jharris1993/PCIe_Floppy_Interface/Reference_Documentation/Research/README.md

# Research

This directory contains project-created research derived from external sources.

Research does not become a current project requirement or design merely because it is recorded here or discussed in `Project_Decisions/`. Current requirements and design are expressed in `Requirements.md` and `Design.md`, respectively.
