jharris1993/PCIe_Floppy_Interface/Reference_Implementations/Greaseweazle/Wiki_Snapshot/assets/f7_slim/F7_Slim_BoM.pdf

## Bill Of Materials for Greaseweazle F7 Basic

Design Title | Greaseweazle F7 Basic
Author | George Rudolf Mezzomo
Document Number | 01
Revision | 2.0
Design Created | segunda-feira, 10 de fevereiro de 2020
Design Last Modified sábado, 19 de dezembro de 2020

### Total Parts In Design 27

0 Modules
Quantity | References | Value
Sub-totals:
15 Capacitors
Quantity | References | Value
9 | C1-C2,C4,C6,C10-C14 | 100n
1 | C3 | 4.7u
3 | C5,C7-C8 | 1.0u
2 | C9,C15 | 10u
Sub-totals:
3 Resistors
Quantity | References | Value
2 | R1-R2 | CAY16
1 | R4 | 470
Sub-totals:
2 Integrated Circuits
Quantity | References | Value
1 | U1 | STM32F730R8T6
1 | U2 | AP2112K-3
Sub-totals:
0 Transistors
Quantity | References | Value
Sub-totals:
0 Diodes
Quantity | References | Value
Sub-totals:
7 Miscellaneous
Quantity | References | Value
1 | ACT | DIODE-LED
1 | DEBUG | CONN-SIL7
1 | J1 | 52271-2669
2 | RESET,WRITE INHIBIT | CONN-SIL2
1 | USB1 | 61729-0010BLF
1 | XO1 | ECS-3225MV-160-BN-TR
Sub-totals:

Totals:

| | sábado, 19 de dezembro de 2020 09:44:36
