jharris1993/PCIe_Floppy_Interface/Reference_Implementations/Greaseweazle/Wiki_Snapshot/assets/adapter_rev1/04_pill_headers.jpg

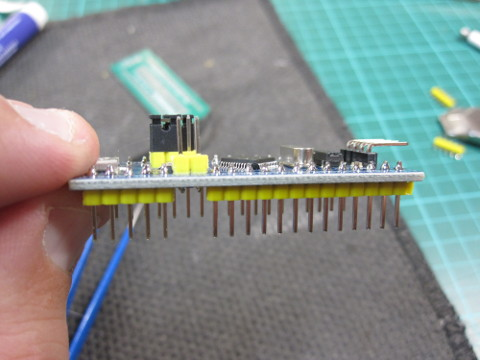
Reference_Implementations/Greaseweazle/Wiki_Snapshot/assets/adapter_rev1/04_pill_headers.jpg
