jharris1993/PCIe_Floppy_Interface/Reference_Implementations/Greaseweazle/Wiki_Snapshot/assets/f7_lightning/00_board.jpg

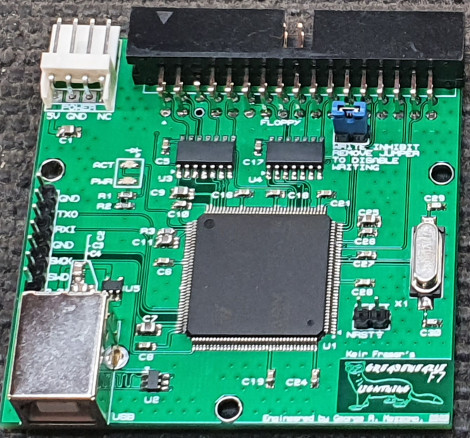
Reference_Implementations/Greaseweazle/Wiki_Snapshot/assets/f7_lightning/00_board.jpg
