jharris1993/PCIe_Floppy_Interface/Reference_Implementations/Greaseweazle/Wiki_Snapshot/assets/f7_lightning_plus/WIN_20200910_11_37_35_Pro.jpg

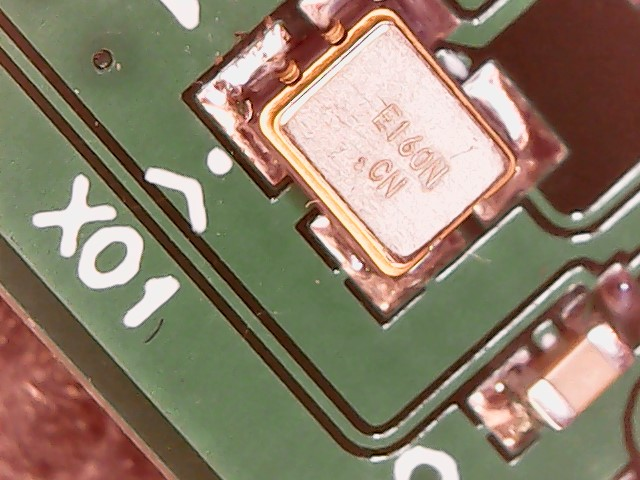
Reference_Implementations/Greaseweazle/Wiki_Snapshot/assets/f7_lightning_plus/WIN_20200910_11_37_35_Pro.jpg
