jharris1993/PCIe_Floppy_Interface/Reference_Implementations/Greaseweazle/Wiki_Snapshot/assets/ibmpc_ribbon.jpg

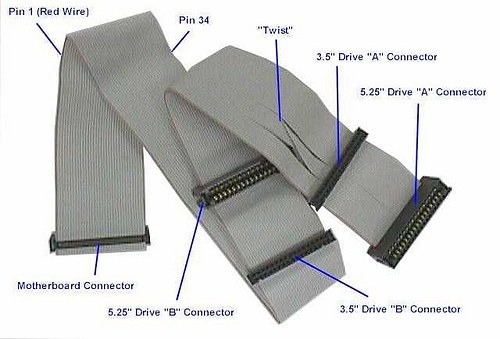
Reference_Implementations/Greaseweazle/Wiki_Snapshot/assets/ibmpc_ribbon.jpg
