jharris1993/PCIe_Floppy_Interface/Reference_Implementations/Greaseweazle/Wiki_Snapshot/assets/adapter_rev1/05_pill_soldered_inuse.jpg

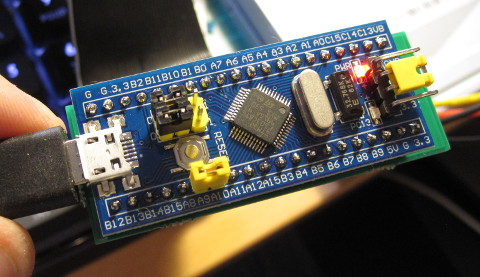
Reference_Implementations/Greaseweazle/Wiki_Snapshot/assets/adapter_rev1/05_pill_soldered_inuse.jpg
