jharris1993/PCIe_Floppy_Interface/Reference_Implementations/Greaseweazle/Wiki_Snapshot/assets/f7_rev1/F7_10_Schematic.pdf

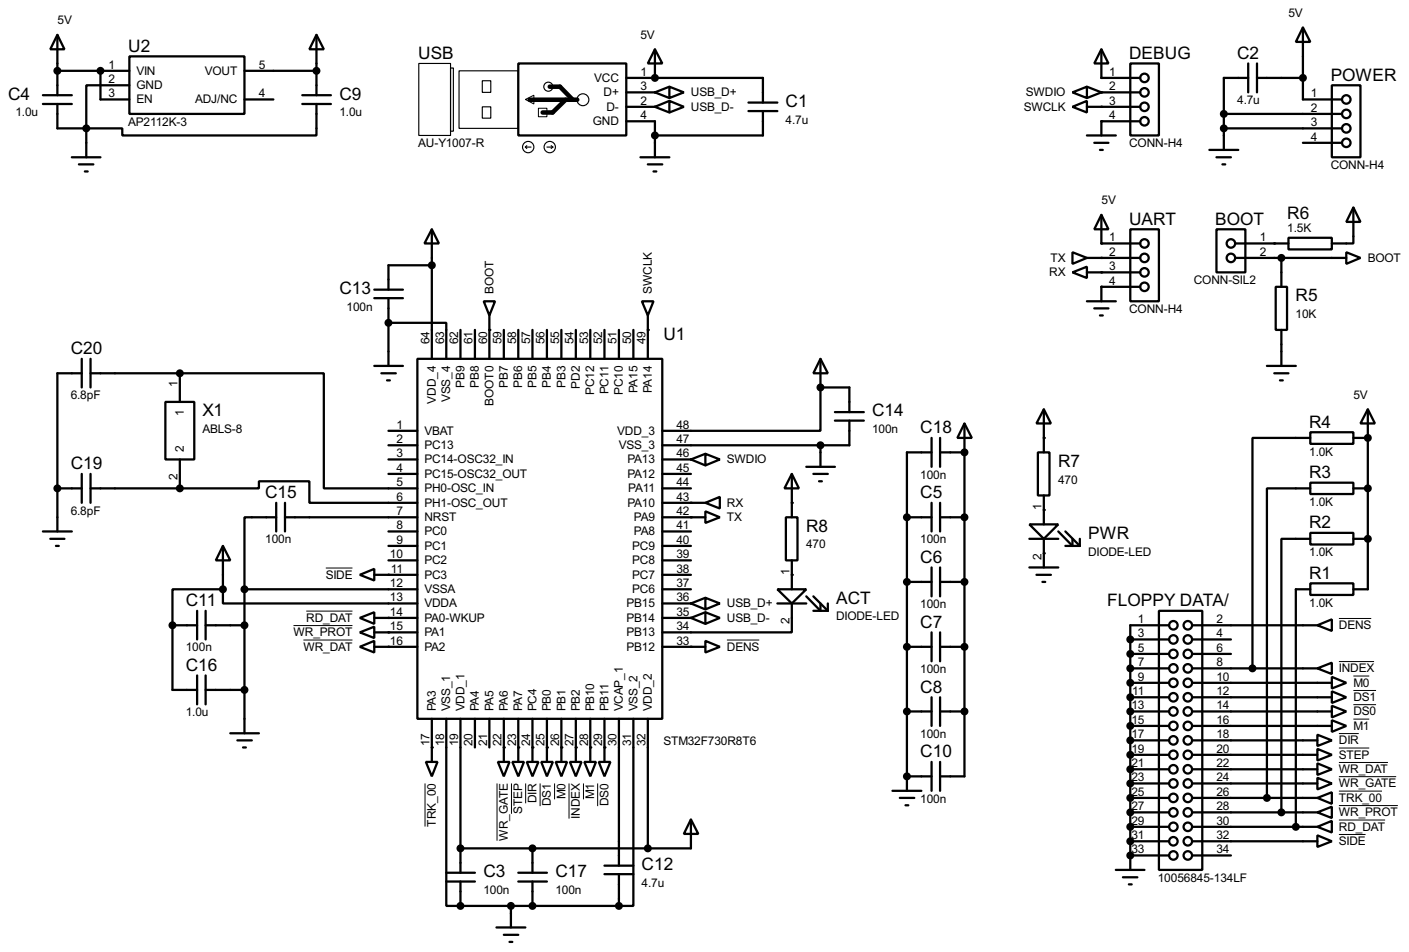
[picture p68: page 1]
