jharris1993/PCIe_Floppy_Interface/Reference_Implementations/Greaseweazle/Wiki_Snapshot/assets/f7_v1.1/F7_11_Schematic.pdf

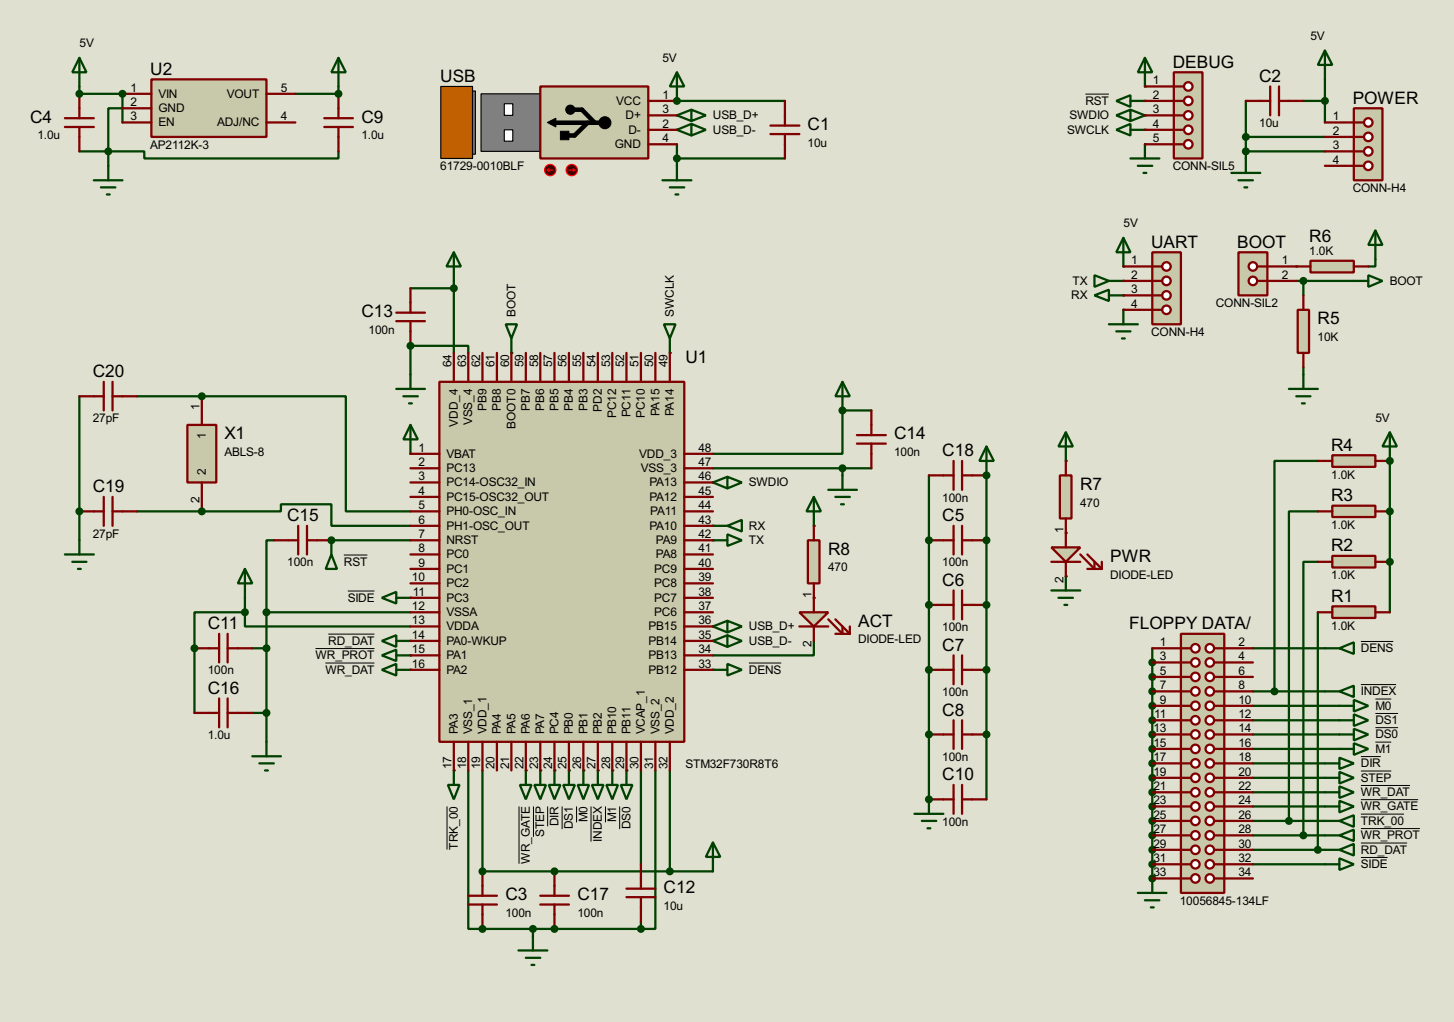
[picture p69: page 1]
